vis3r/Headset_3D_Designs/Official_Headset/STL_Files/Main_Body/Left_Hand_Frame_191005-01.stl

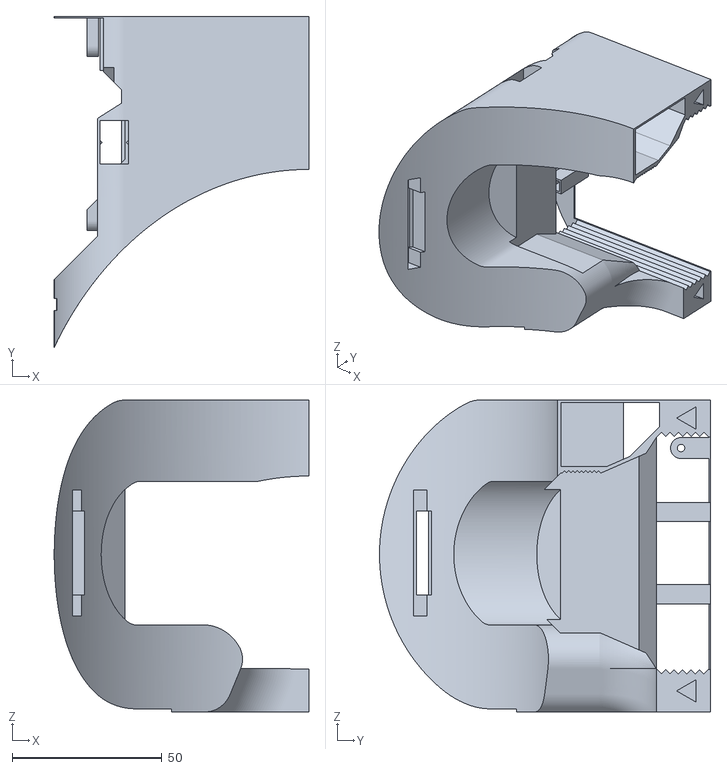
[picture p12: CAD file, 2019-10-05]
Official_Headset/STL_Files/Main_Body/Left_Hand_Frame_191005-01.stl
84.9 x 110.4 x 104.0
