vis3r/Headset_3D_Designs/Official_Headset/STL_Files/Visual_Guide_&_Screen_Holder/Visual_Guide_190924-01.stl

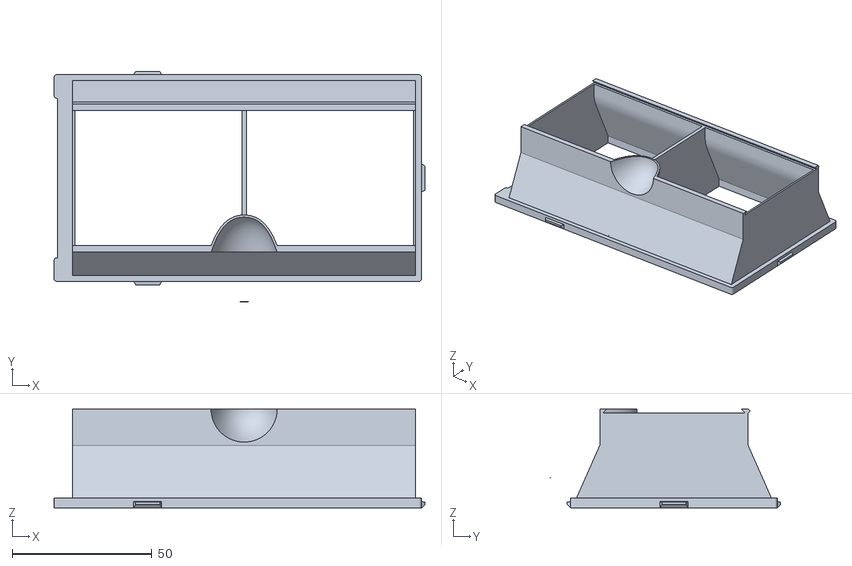
[picture p13: CAD file, 2019-09-25]
Official_Headset/STL_Files/Visual_Guide_&_Screen_Holder/Visual_Guide_190924-01.stl
132.6 x 82.3 x 35.4
