vis3r/Headset_3D_Designs/Official_Headset/STL_Files/Main_Body/Right_Hand_Frame_191002-01.stl

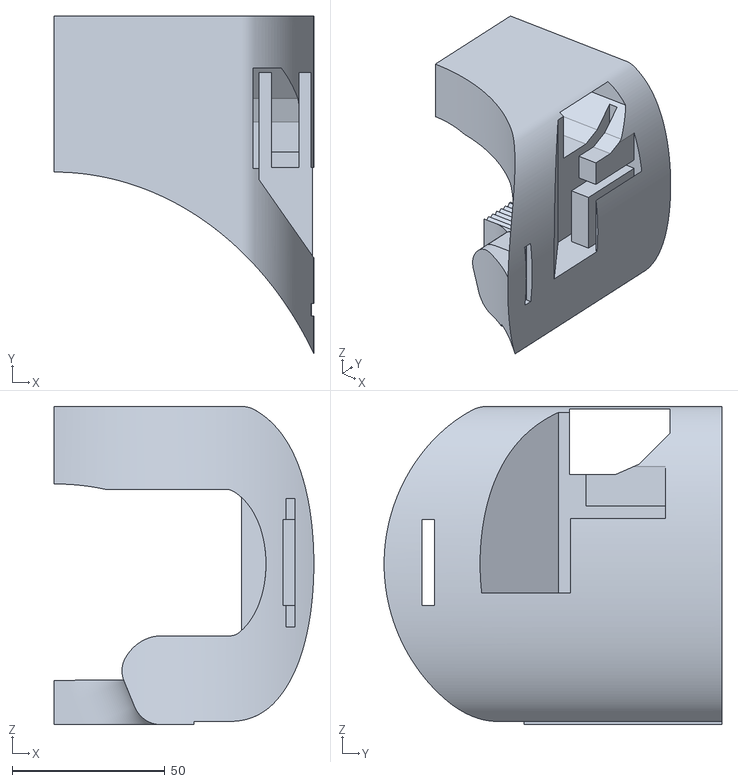
[picture p14: CAD file, 2019-10-02]
Official_Headset/STL_Files/Main_Body/Right_Hand_Frame_191002-01.stl
84.9 x 110.5 x 104.0
